LaureWOLFF/2526_Maker_CasqueBluetooth/TDs/CAO/CAO ressort.jpg

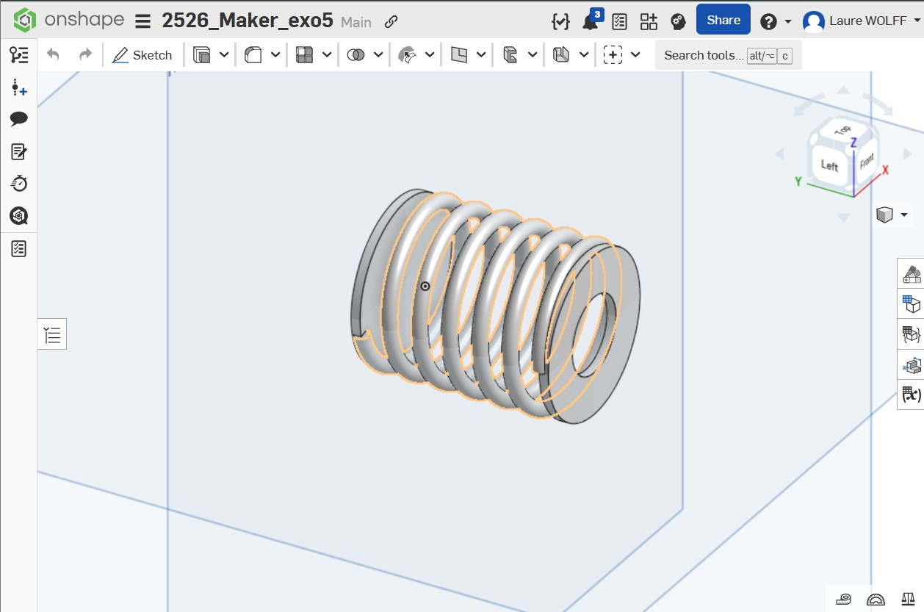
TDs/CAO/CAO ressort.jpg
