LaureWOLFF/2526_Maker_CasqueBluetooth/TDs/CAO/CAO support téléphone.jpg

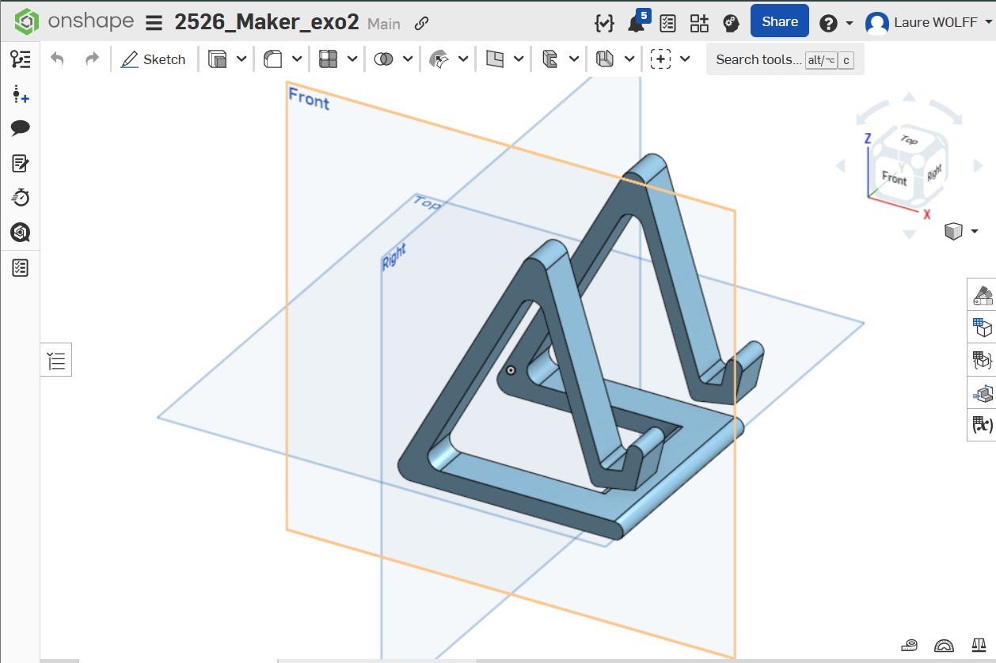
TDs/CAO/CAO support téléphone.jpg
