LaureWOLFF/2526_Maker_CasqueBluetooth/TDs/CAO/CAO support.jpg

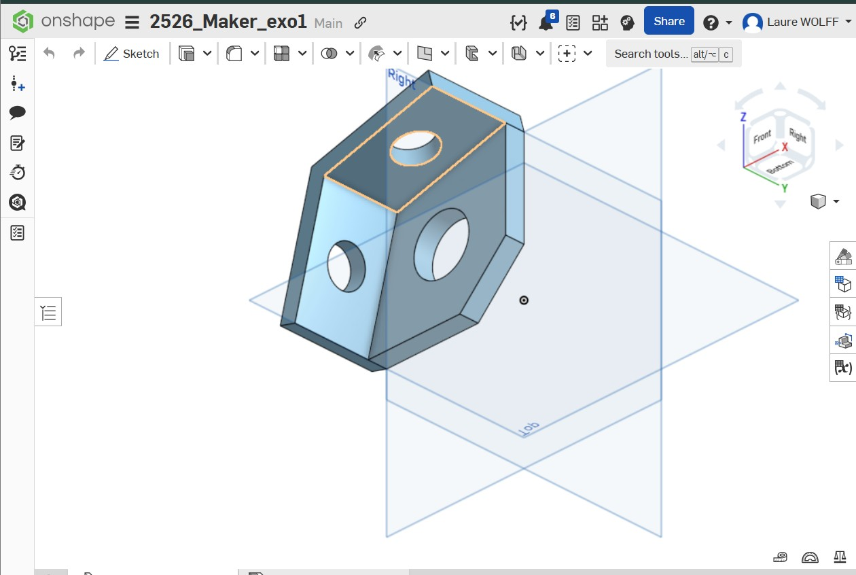
TDs/CAO/CAO support.jpg
