LaureWOLFF/2526_Maker_CasqueBluetooth/TDs/impressions 3D et couture/WhatsApp Image 2026-05-05 at 10.13.27.jpeg

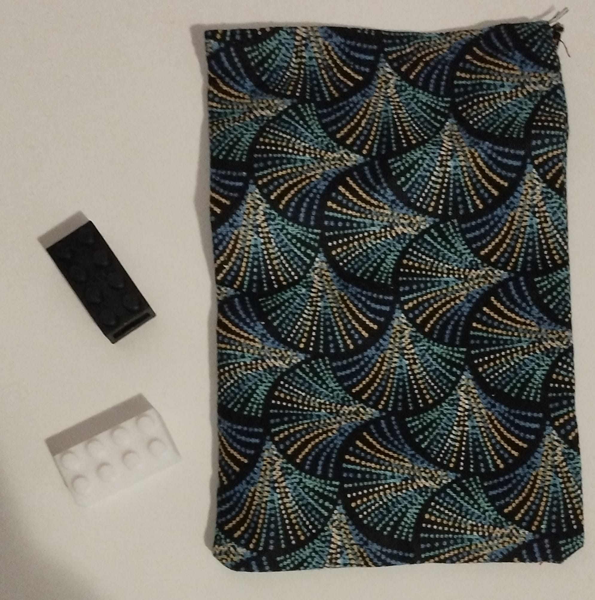
TDs/impressions 3D et couture/WhatsApp Image 2026-05-05 at 10.13.27.jpeg
