LaureWOLFF/2526_Maker_CasqueBluetooth/PCB_Casque/DacAmpli1.kicad_sch

## KiCad design PCB_Casque/DacAmpli1.kicad_sch (2026-03-19)

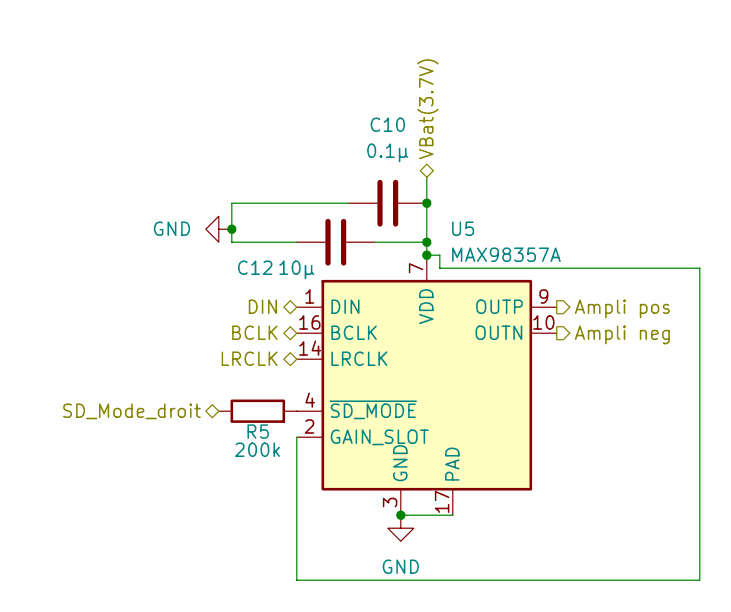
[picture p14: schematic DacAmpli1.kicad_sch]

Parts:
C10: 0.1µ; C_0402_1005Metric_Pad0.74x0.62mm_HandSolder
C12: 10µ; C_0603_1608Metric_Pad1.08x0.95mm_HandSolder
R5: 200k; R_0402_1005Metric_Pad0.72x0.64mm_HandSolder
U5: MAX98357A; TQFN-16-1EP_3x3mm_P0.5mm_EP1.23x1.23mm

Connections:
Ampli neg: U5.10 (OUTN)
Ampli pos: U5.9 (OUTP)
BCLK: U5.16 (BCLK)
DIN: U5.1 (DIN)
GND: C10.2, C12.2, U5.3 (GND), U5.11 (GND), U5.15 (GND), U5.17 (PAD)
LRCLK: U5.14 (LRCLK)
unnamed: R5.2, U5.4 (~SD_MODE)
SD_Mode_droit: R5.1
VBat(3.7V): C10.1, C12.1, U5.2 (GAIN_SLOT), U5.7 (VDD), U5.8 (VDD)
