LaureWOLFF/2526_Maker_CasqueBluetooth/PCB_Casque/DacAmpli.kicad_sch

## KiCad design PCB_Casque/DacAmpli.kicad_sch (2026-03-19)

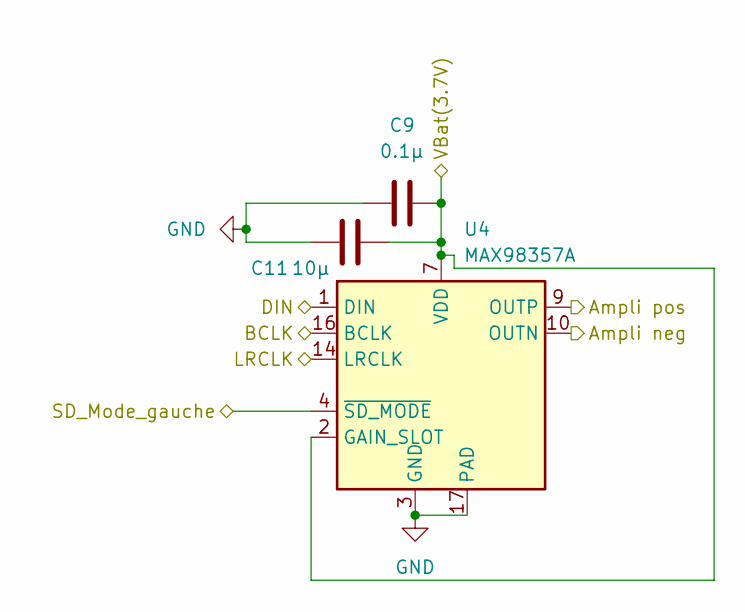
[picture p15: schematic DacAmpli.kicad_sch]

Parts:
C9: 0.1µ; C_0402_1005Metric_Pad0.74x0.62mm_HandSolder
C11: 10µ; C_0603_1608Metric_Pad1.08x0.95mm_HandSolder
U4: MAX98357A; TQFN-16-1EP_3x3mm_P0.5mm_EP1.23x1.23mm

Connections:
Ampli neg: U4.10 (OUTN)
Ampli pos: U4.9 (OUTP)
BCLK: U4.16 (BCLK)
DIN: U4.1 (DIN)
GND: C9.2, C11.2, U4.3 (GND), U4.11 (GND), U4.15 (GND), U4.17 (PAD)
LRCLK: U4.14 (LRCLK)
SD_Mode_gauche: U4.4 (~SD_MODE)
VBat(3.7V): C9.1, C11.1, U4.2 (GAIN_SLOT), U4.7 (VDD), U4.8 (VDD)
