LaureWOLFF/2526_Maker_CasqueBluetooth/PCB_Casque/ESP23_s3_mini_1_N8.kicad_sch

## KiCad design PCB_Casque/ESP23_s3_mini_1_N8.kicad_sch (2026-03-23)

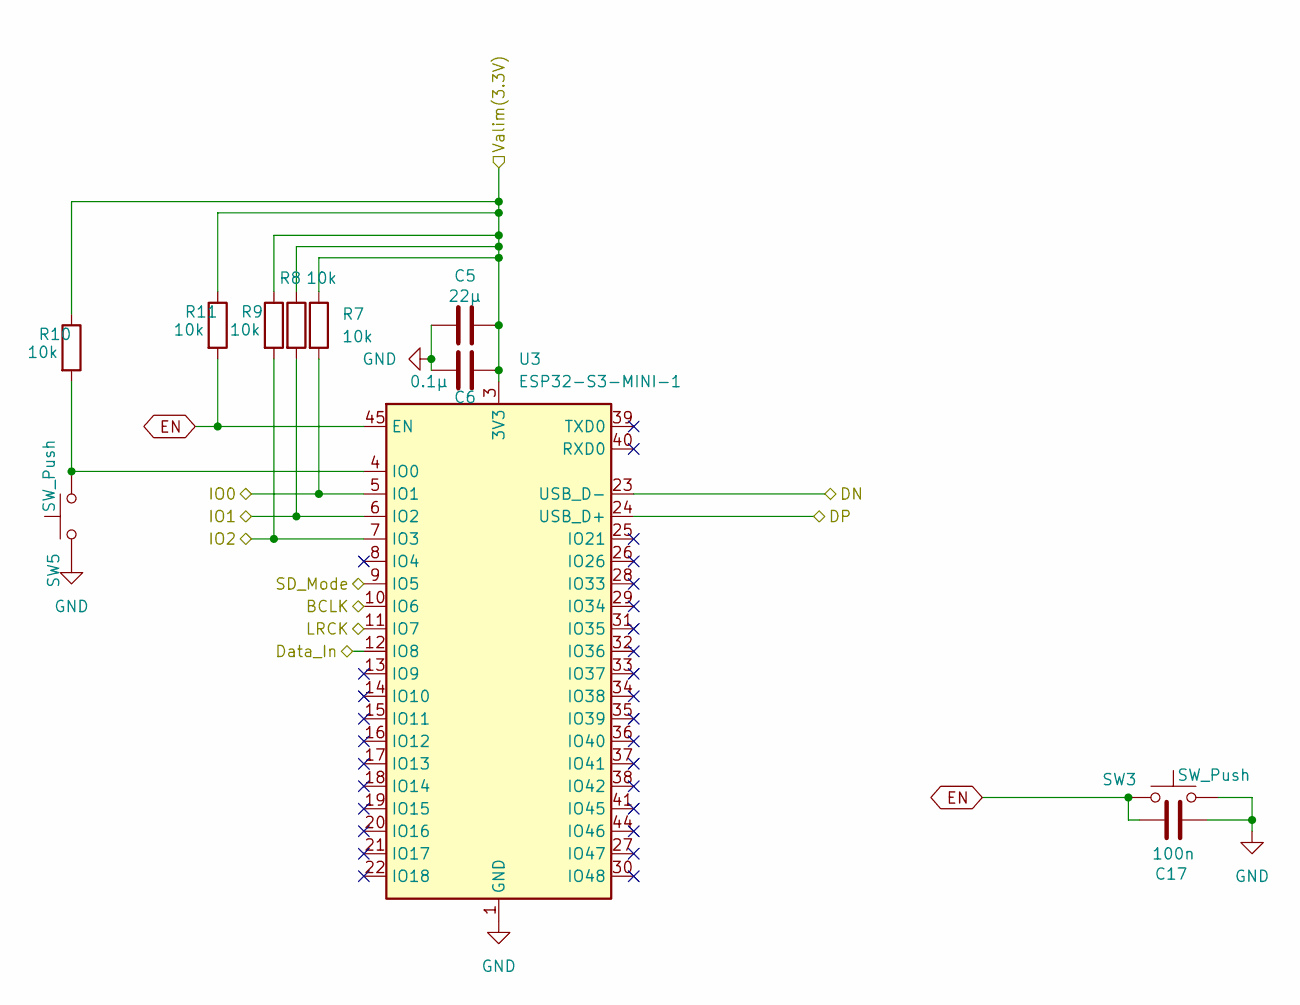
[picture p16: schematic ESP23_s3_mini_1_N8.kicad_sch]

Parts:
C5: 22µ; C_0603_1608Metric_Pad1.08x0.95mm_HandSolder
C6: 0.1µ; C_0402_1005Metric_Pad0.74x0.62mm_HandSolder
C17: 100n; C_0402_1005Metric_Pad0.74x0.62mm_HandSolder
R7, R8, R9, R10, R11: 10k; R_0402_1005Metric_Pad0.72x0.64mm_HandSolder
SW3, SW5: SW_Push; 435171014816
U3: ESP32-S3-MINI-1; ESP32-S2-MINI-1

Connections:
BCLK: U3.10 (IO6)
DN: U3.23 (USB_D-)
DP: U3.24 (USB_D+)
Data_In: U3.12 (IO8)
EN: C17.2, R11.2, SW3.1, U3.45 (EN)
GND: C5.2, C6.1, C17.1, SW3.2, SW5.1, U3.1 (GND), U3.2 (GND), U3.42 (GND), U3.43 (GND), U3.46 (GND), U3.47 (GND), U3.48 (GND), U3.49 (GND), U3.50 (GND), U3.51 (GND), U3.52 (GND), U3.53 (GND), U3.54 (GND), U3.55 (GND), U3.56 (GND), U3.57 (GND), U3.58 (GND), U3.59 (GND), U3.60 (GND), U3.61 (GND), U3.62 (GND), U3.63 (GND), U3.64 (GND), U3.65 (GND)
IO0: R7.2, U3.5 (IO1)
IO1: R8.2, U3.6 (IO2)
IO2: R9.2, U3.7 (IO3)
LRCK: U3.11 (IO7)
unnamed: R10.2, SW5.2, U3.4 (IO0)
SD_Mode: U3.9 (IO5)
Valim(3.3V): C5.1, C6.2, R7.1, R8.1, R9.1, R10.1, R11.1, U3.3 (3V3)
