LaureWOLFF/2526_Maker_CasqueBluetooth/PCB_Casque/USB_c.kicad_sch

## KiCad design PCB_Casque/USB_c.kicad_sch (2026-03-23)

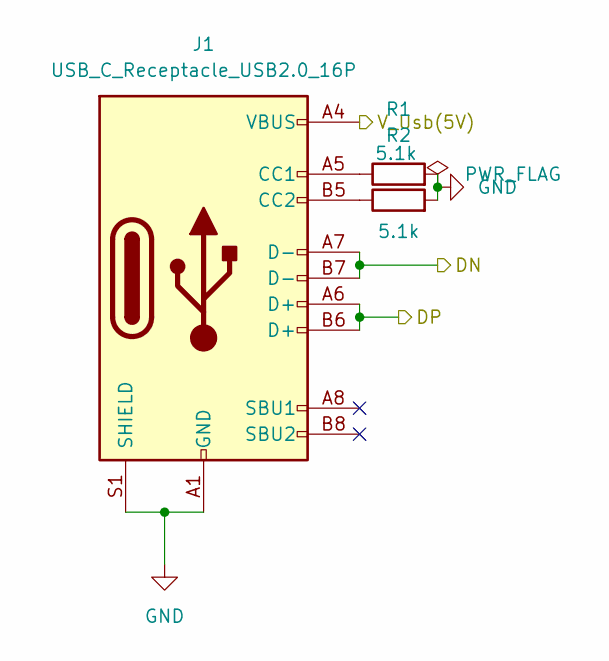
[picture p17: schematic USB_c.kicad_sch]

Parts:
J1: USB_C_Receptacle_USB2.0_16P; USB_C_Receptacle_GCT_USB4105-xx-A_16P_TopMnt_Horizontal
R1, R2: 5.1k; R_0402_1005Metric_Pad0.72x0.64mm_HandSolder

Connections:
DN: J1.A7 (D-), J1.B7 (D-)
DP: J1.A6 (D+), J1.B6 (D+)
GND: J1.A1 (GND), J1.A12 (GND), J1.B1 (GND), J1.B12 (GND), J1.S1 (SHIELD), R1.2, R2.2
unnamed: J1.A5 (CC1), R1.1
unnamed: J1.B5 (CC2), R2.1
V_Usb(5V): J1.A4 (VBUS), J1.A9 (VBUS), J1.B4 (VBUS), J1.B9 (VBUS)
