LaureWOLFF/2526_Maker_CasqueBluetooth/PCB_Casque/abaisseur.kicad_sch

## KiCad design PCB_Casque/abaisseur.kicad_sch (2026-03-19)

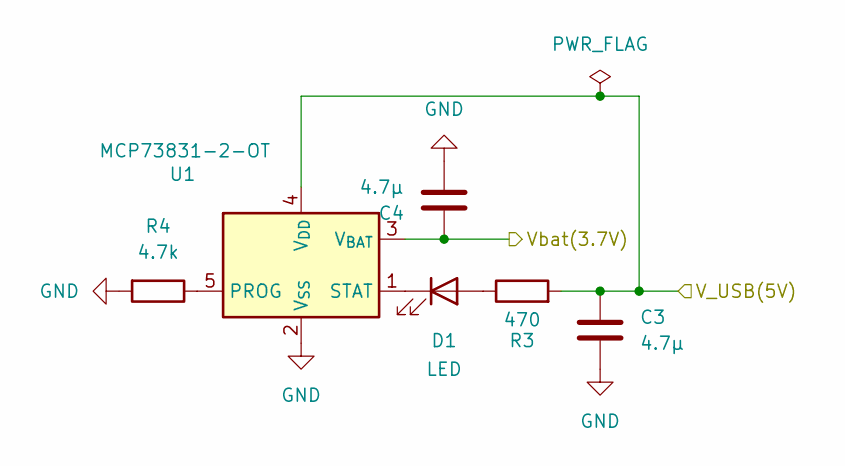
[picture p18: schematic abaisseur.kicad_sch]

Parts:
C3, C4: 4.7µ; C_0402_1005Metric_Pad0.74x0.62mm_HandSolder
D1: LED; LED_0603_1608Metric_Pad1.05x0.95mm_HandSolder
R3: 470; R_0402_1005Metric_Pad0.72x0.64mm_HandSolder
R4: 4.7k; R_0402_1005Metric_Pad0.72x0.64mm_HandSolder
U1: MCP73831-2-OT; SOT-23-5

Connections:
GND: C3.2, C4.2, R4.2, U1.2 (V_{SS})
unnamed: D1.1 (K), U1.1 (STAT)
unnamed: D1.2 (A), R3.1
unnamed: R4.1, U1.5 (PROG)
V_USB(5V): C3.1, R3.2, U1.4 (V_{DD})
Vbat(3.7V): C4.1, U1.3 (V_{BAT})
