LaureWOLFF/2526_Maker_CasqueBluetooth/PCB_Casque/boutons.kicad_sch

## KiCad design PCB_Casque/boutons.kicad_sch (2026-03-19)

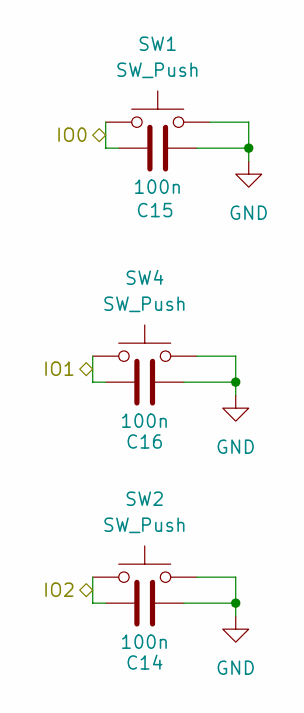
[picture p19: schematic boutons.kicad_sch]

Parts:
C14, C15, C16: 100n; C_0402_1005Metric_Pad0.74x0.62mm_HandSolder
SW1, SW2, SW4: SW_Push; SW_Tactile_SPST_Angled_PTS645Vx58-2LFS

Connections:
GND: C14.1, C15.1, C16.1, SW1.2, SW2.2, SW4.2
IO0: C15.2, SW1.1
IO1: C16.2, SW4.1
IO2: C14.2, SW2.1
