LaureWOLFF/2526_Maker_CasqueBluetooth/PCB_Casque/hautparleurs.kicad_sch

## KiCad design PCB_Casque/hautparleurs.kicad_sch (2026-03-19)

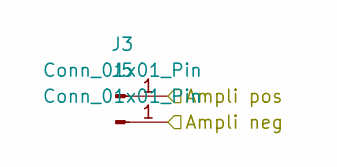
[picture p20: schematic hautparleurs.kicad_sch]

Parts:
J3, J5: Conn_01x01_Pin; TestPoint_Pad_D2.0mm

Connections:
Ampli neg: J5.1
Ampli pos: J3.1
