LaureWOLFF/2526_Maker_CasqueBluetooth/PCB_Casque/regulateur.kicad_sch

## KiCad design PCB_Casque/regulateur.kicad_sch (2026-03-19)

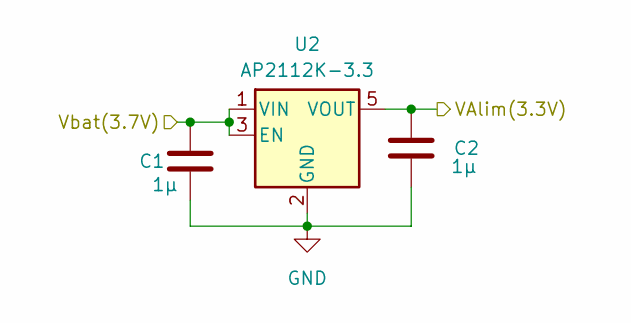
[picture p21: schematic regulateur.kicad_sch]

Parts:
C1, C2: 1µ; C_0402_1005Metric_Pad0.74x0.62mm_HandSolder
U2: AP2112K-3.3; SOT-23-5

Connections:
GND: C1.2, C2.2, U2.2 (GND)
VAlim(3.3V): C2.1, U2.5 (VOUT)
Vbat(3.7V): C1.1, U2.1 (VIN), U2.3 (EN)
