LaureWOLFF/2526_Maker_CasqueBluetooth/PCB_Casque/trou_fixation.kicad_sch

## KiCad design PCB_Casque/trou_fixation.kicad_sch (2026-03-23)

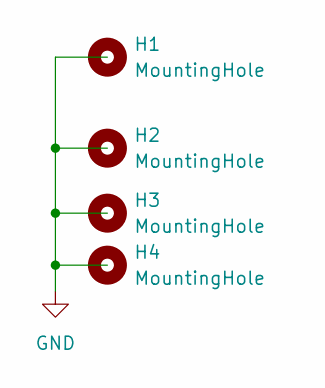
[picture p22: schematic trou_fixation.kicad_sch]

Parts:
H1, H2, H3, H4: MountingHole; MountingHole_2.7mm_M2.5
